telzo2000/cool756/img/img00004.jpg

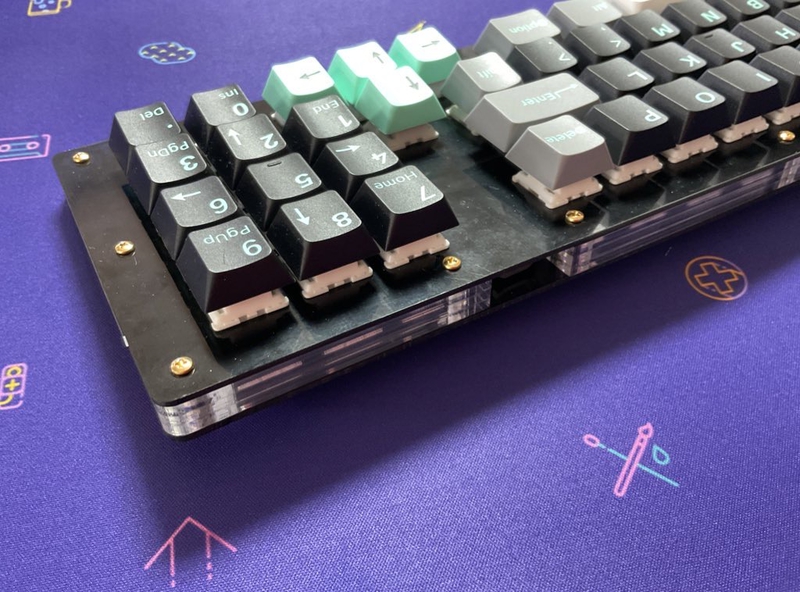
img/img00004.jpg
