telzo2000/cool756/img/img00006.jpg

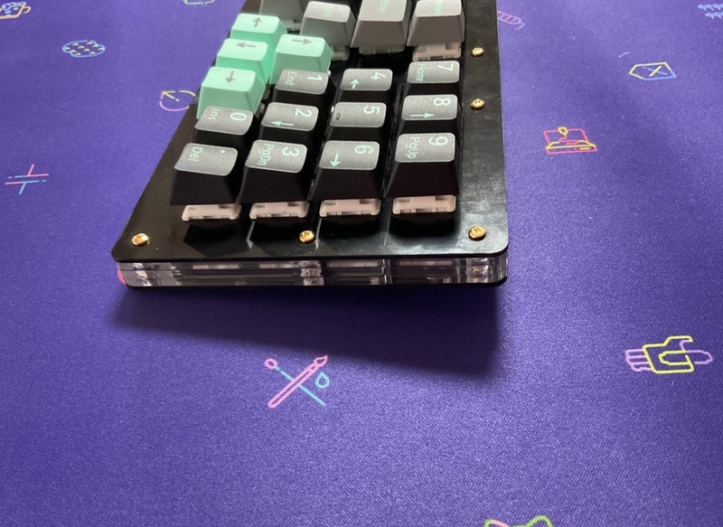
img/img00006.jpg
