telzo2000/cool756/img/img00016.jpg

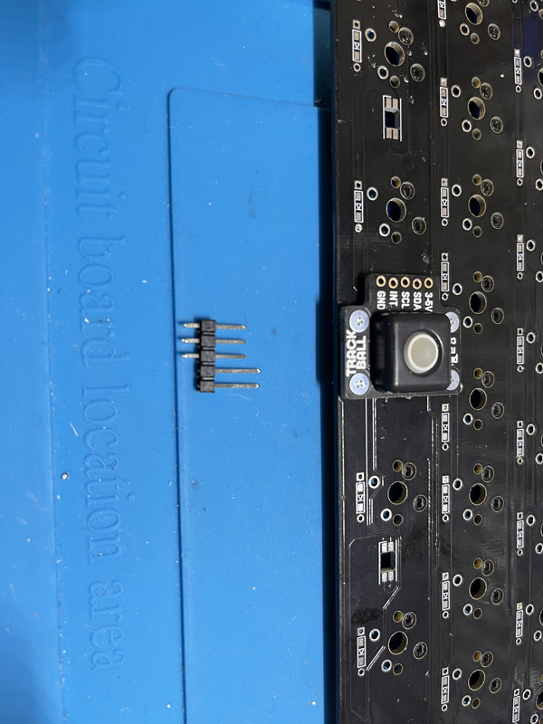
img/img00016.jpg
